KMedon/Beep_flag/Ostateczna wersja_nadajnik/SubGHz_Phy/App/subghz_phy_app.h

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

/* Define to prevent recursive inclusion -------------------------------------*/
#ifndef __SUBGHZ_PHY_APP_H__
#define __SUBGHZ_PHY_APP_H__

#ifdef __cplusplus
extern "C" {
#endif

/* Includes ------------------------------------------------------------------*/
/* USER CODE BEGIN Includes */
#define LED_ON 0
#define LED_OFF 1
/* USER CODE END Includes */

/* Exported types ------------------------------------------------------------*/
/* Exported constants --------------------------------------------------------*/
/* MODEM type: one shall be 1 the other shall be 0 */
#define USE_MODEM_LORA  1
#define USE_MODEM_FSK   0

#define RF_FREQUENCY                                868000000 /* Hz */

#ifndef TX_OUTPUT_POWER   /* please, to change this value, redefine it in USER CODE SECTION */
#define TX_OUTPUT_POWER                             14        /* dBm */
#endif /* TX_OUTPUT_POWER */

#if (( USE_MODEM_LORA == 1 ) && ( USE_MODEM_FSK == 0 ))
#define LORA_BANDWIDTH                              0         /* [0: 125 kHz, 1: 250 kHz, 2: 500 kHz, 3: Reserved] */
#define LORA_SPREADING_FACTOR                       7         /* [SF7..SF12] */
#define LORA_CODINGRATE                             1         /* [1: 4/5, 2: 4/6, 3: 4/7, 4: 4/8] */
#define LORA_PREAMBLE_LENGTH                        8         /* Same for Tx and Rx */
#define LORA_SYMBOL_TIMEOUT                         5         /* Symbols */
#define LORA_FIX_LENGTH_PAYLOAD_ON                  false
#define LORA_IQ_INVERSION_ON                        false

#elif (( USE_MODEM_LORA == 0 ) && ( USE_MODEM_FSK == 1 ))

#define FSK_FDEV                                    25000     /* Hz */
#define FSK_DATARATE                                50000     /* bps */
#define FSK_BANDWIDTH                               50000     /* Hz */
#define FSK_PREAMBLE_LENGTH                         5         /* Same for Tx and Rx */
#define FSK_FIX_LENGTH_PAYLOAD_ON                   false

#else
#error "Please define a modem in the compiler subghz_phy_app.h."
#endif /* USE_MODEM_LORA | USE_MODEM_FSK */

#define PAYLOAD_LEN                                 64

/* External variables --------------------------------------------------------*/
/* Exported macros -----------------------------------------------------------*/
/* Exported functions prototypes ---------------------------------------------*/
/**
  * @brief  Init Subghz Application
  */
void SubghzApp_Init(void);

#ifdef __cplusplus
}
#endif

#endif /*__SUBGHZ_PHY_APP_H__*/
